11mbs/pipette-tip-sorter/images/(13) Pipettes in the box.jpg

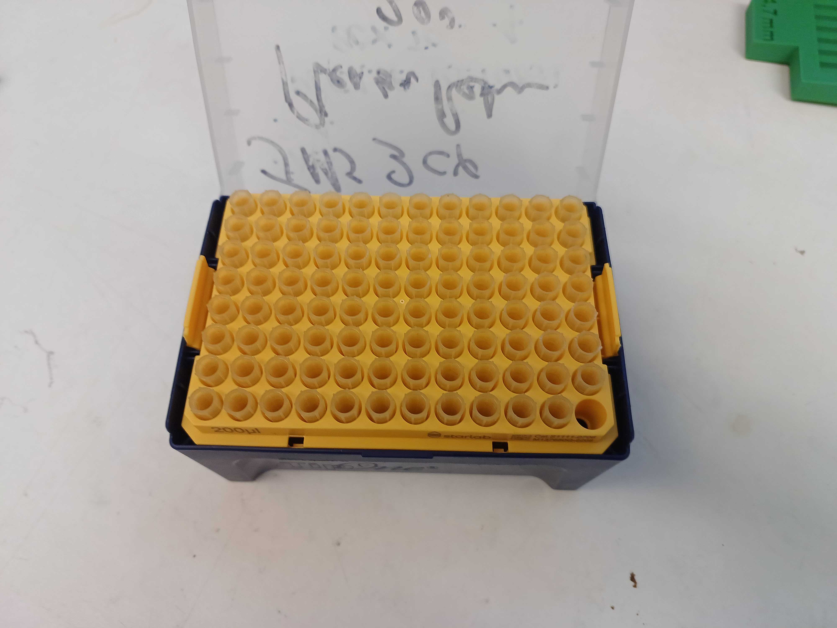
images/(13) Pipettes in the box.jpg
